TrulyVagabond/FullBringer/assets/art5.jpg

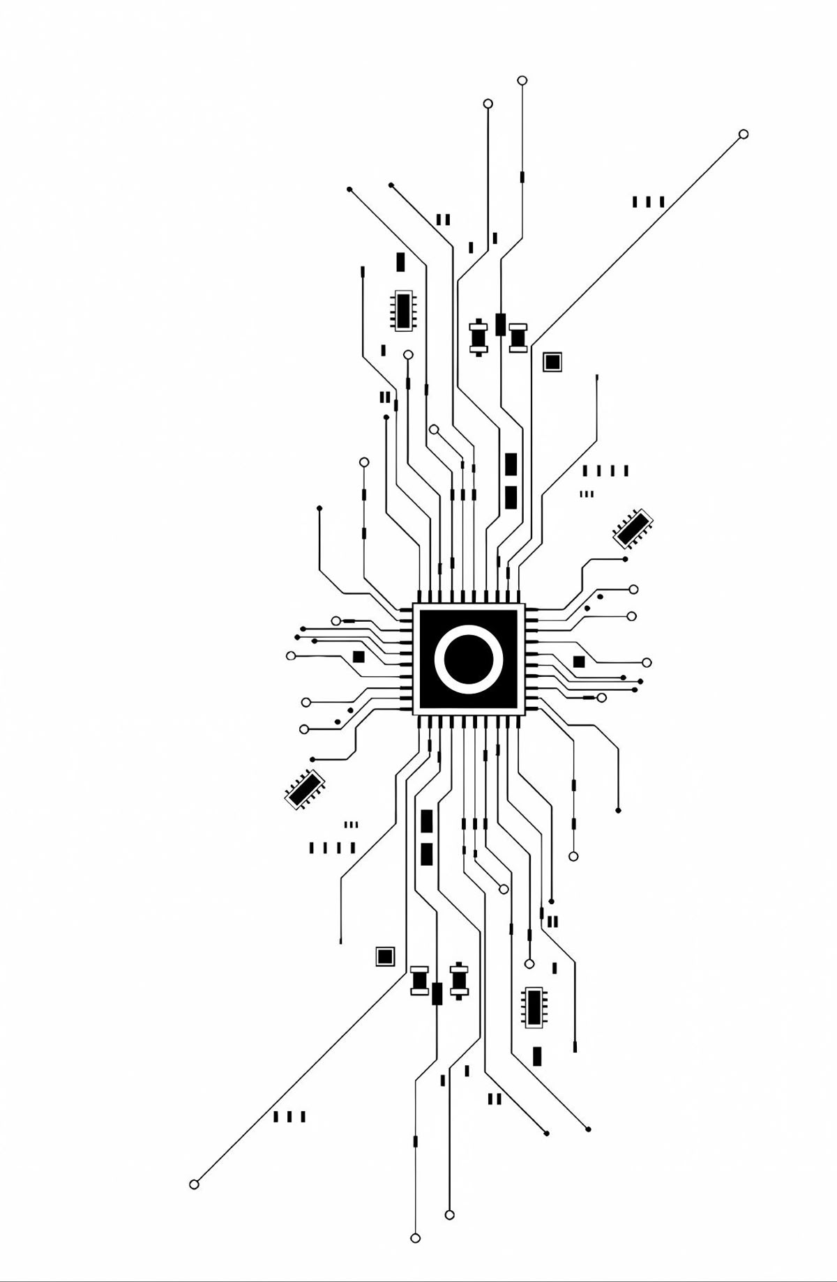
assets/art5.jpg
