TrulyVagabond/FullBringer/assets/art6.jpg

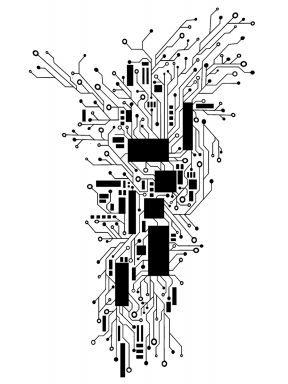
assets/art6.jpg
