TrulyVagabond/FullBringer/assets/QR.png

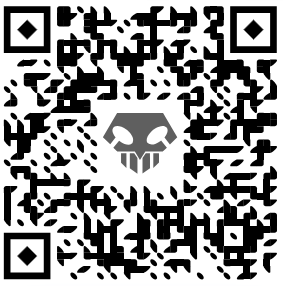
assets/QR.png
